nicolacimmino/PLC-14500/documentation/kit/rev.b/Kit Sleeve Back.pdf

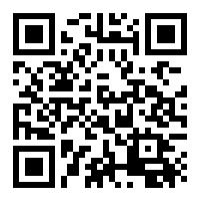
[picture p5: figure]

https://github.com/nicolacimmino/PLC-14500
