nicolacimmino/PLC-14500/_docs/board.jpg

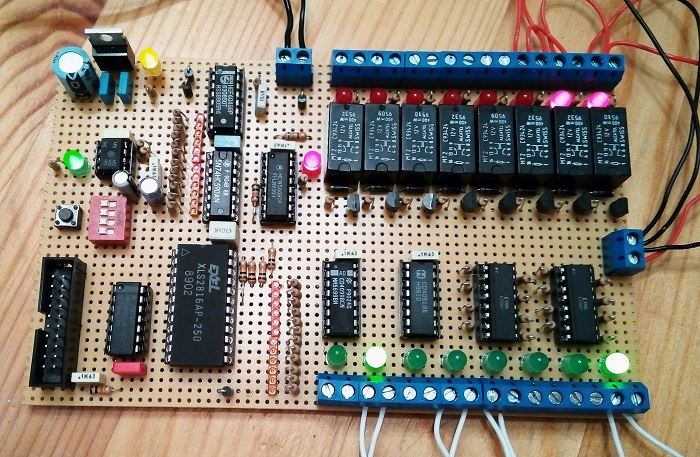
_docs/board.jpg
