nicolacimmino/PLC-14500/documentation/board.png

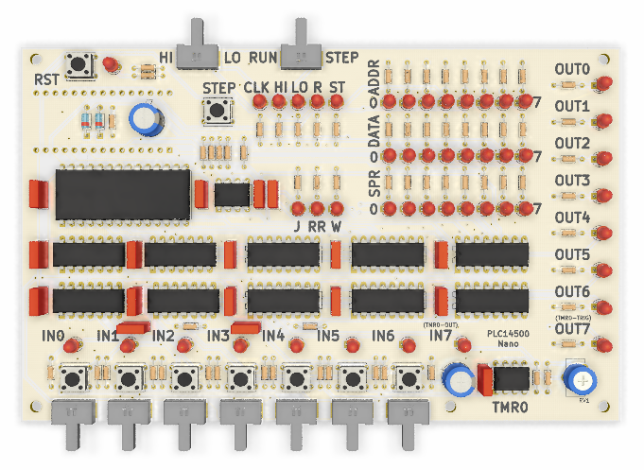
documentation/board.png
