nicolacimmino/PLC-14500/documentation/board_black_revd.png

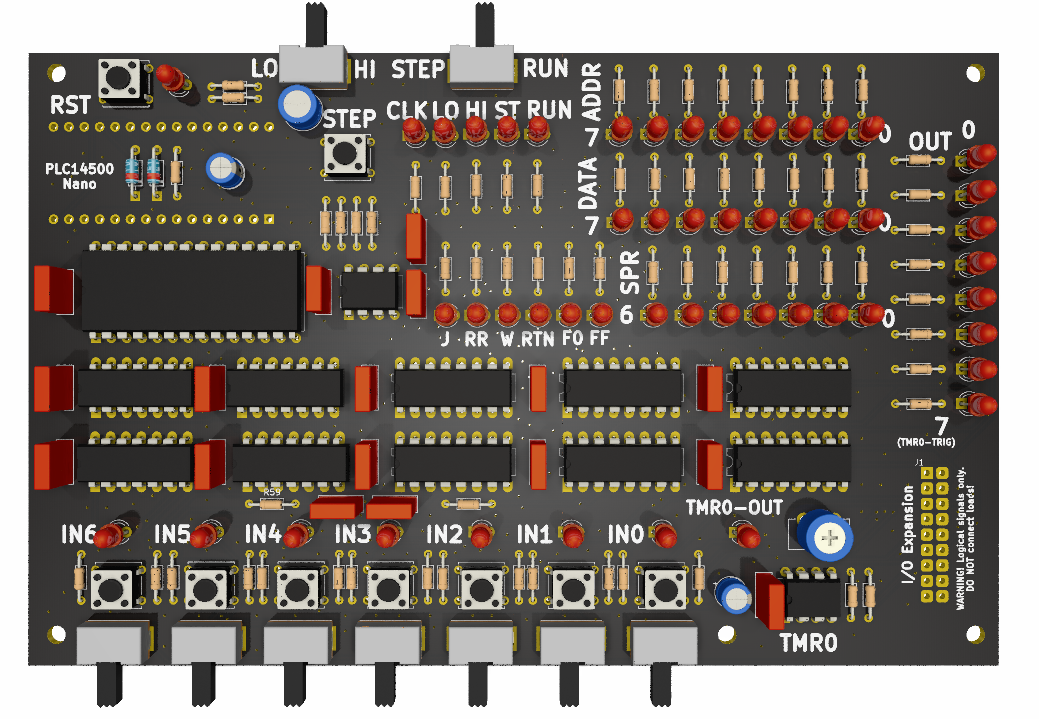
documentation/board_black_revd.png
