nicolacimmino/PLC-14500/documentation/board_green_revc.png

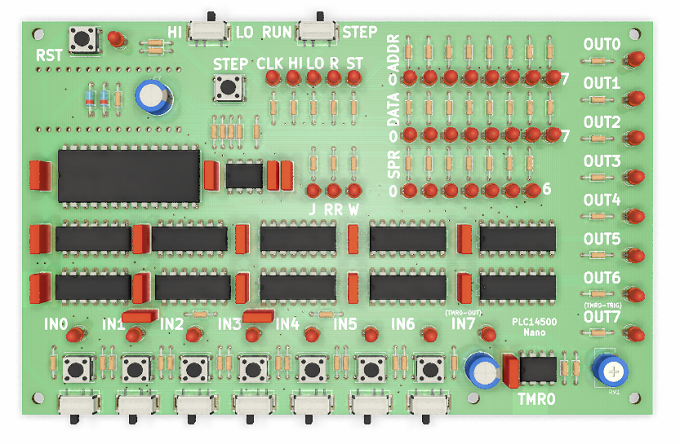
documentation/board_green_revc.png
