nicolacimmino/PLC-14500/documentation/board_white_revc.png

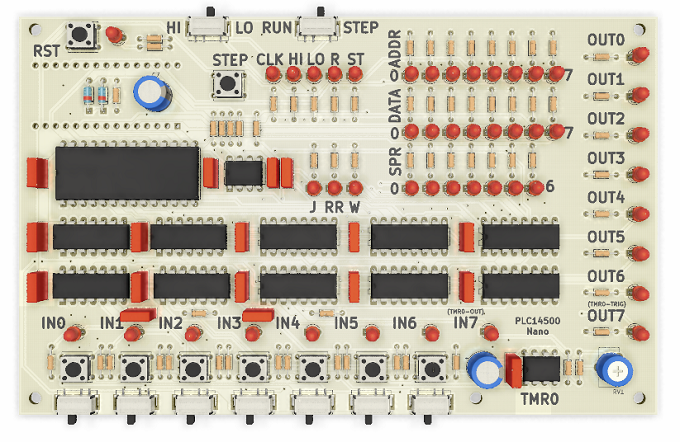
documentation/board_white_revc.png
