nicolacimmino/PLC-14500/documentation/ex1_load_and_store.png

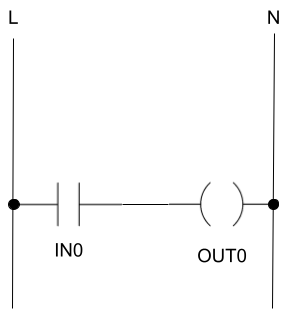
documentation/ex1_load_and_store.png
