nicolacimmino/PLC-14500/documentation/ex3_latch.png

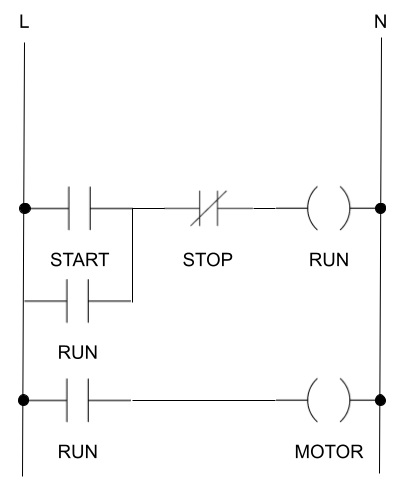
documentation/ex3_latch.png
