nicolacimmino/PLC-14500/documentation/ladder_coil.png

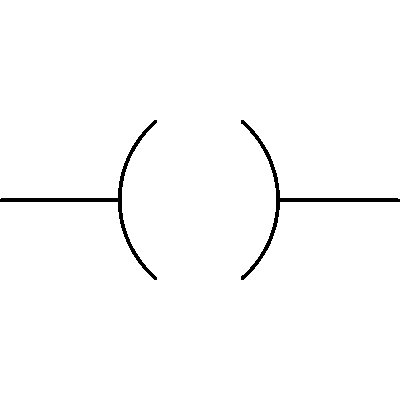
documentation/ladder_coil.png
