nicolacimmino/PLC-14500/documentation/ladder_nc.png

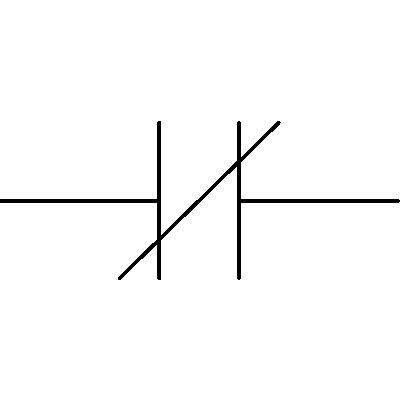
documentation/ladder_nc.png
