nicolacimmino/PLC-14500/documentation/oshw_cert.png

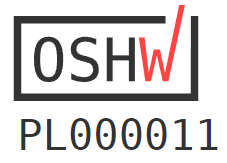
documentation/oshw_cert.png
