nicolacimmino/PLC-14500/documentation/Output.png

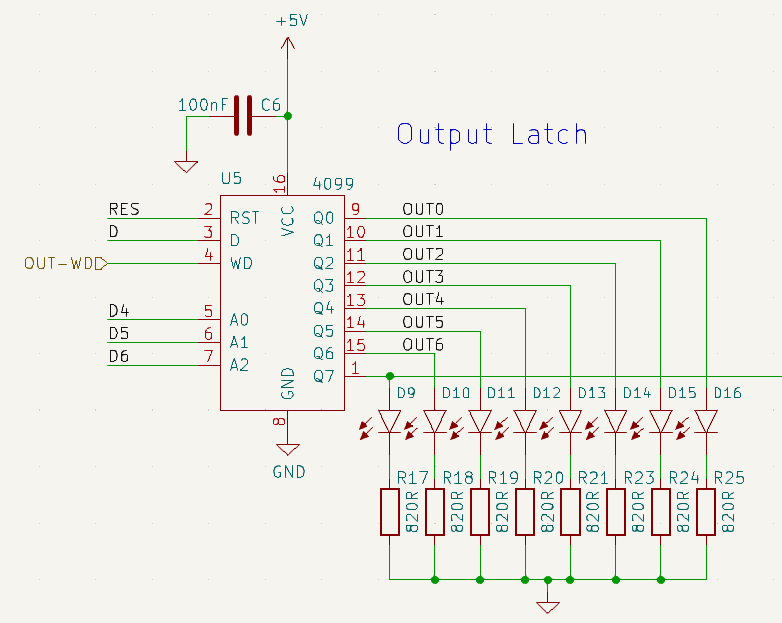
documentation/Output.png
