nicolacimmino/PLC-14500/documentation/pc_memory_icu.png

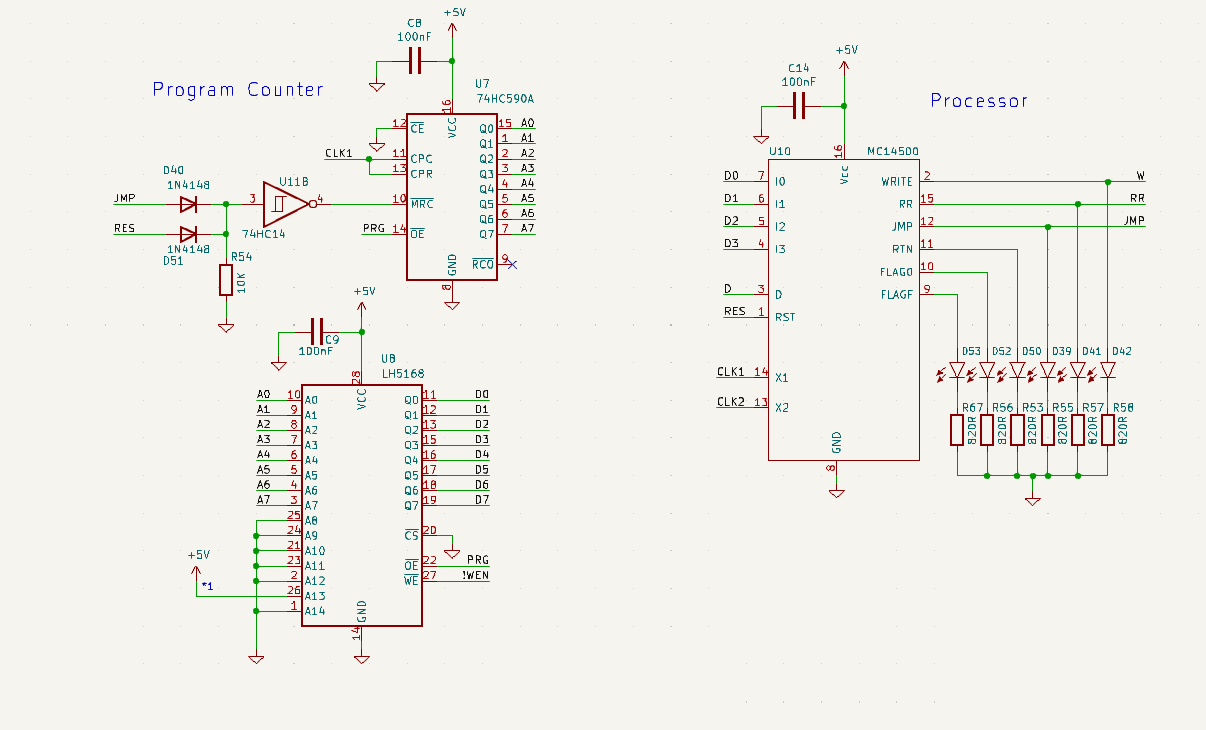
documentation/pc_memory_icu.png
