nicolacimmino/PLC-14500/documentation/PLC14500-Nano_IO_Map.png

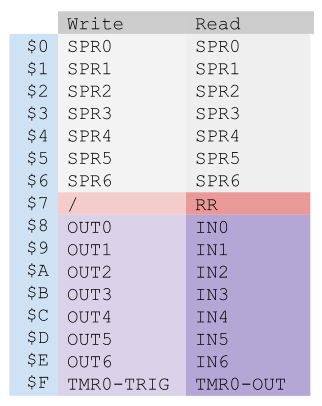
documentation/PLC14500-Nano_IO_Map.png
