nicolacimmino/PLC-14500/documentation/Pulse.png

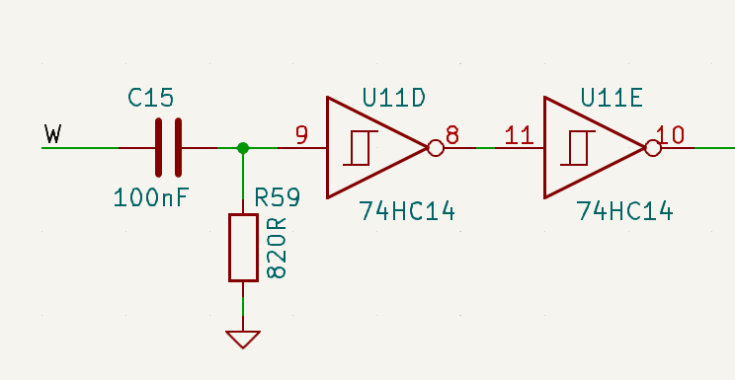
documentation/Pulse.png
