nicolacimmino/PLC-14500/documentation/scop_wp_d4.png

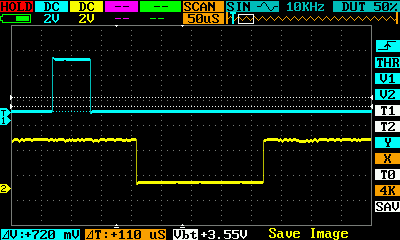
documentation/scop_wp_d4.png
