nicolacimmino/PLC-14500/documentation/scope_w_d4.png

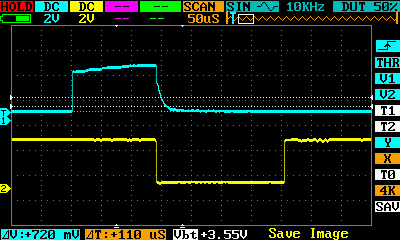
documentation/scope_w_d4.png
