nicolacimmino/PLC-14500/documentation/scope_w_wp.png

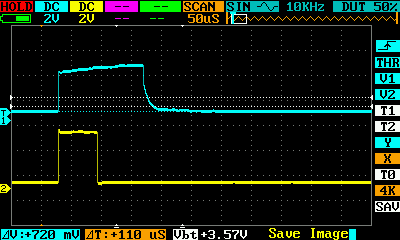
documentation/scope_w_wp.png
