nicolacimmino/PLC-14500/documentation/simulator.png

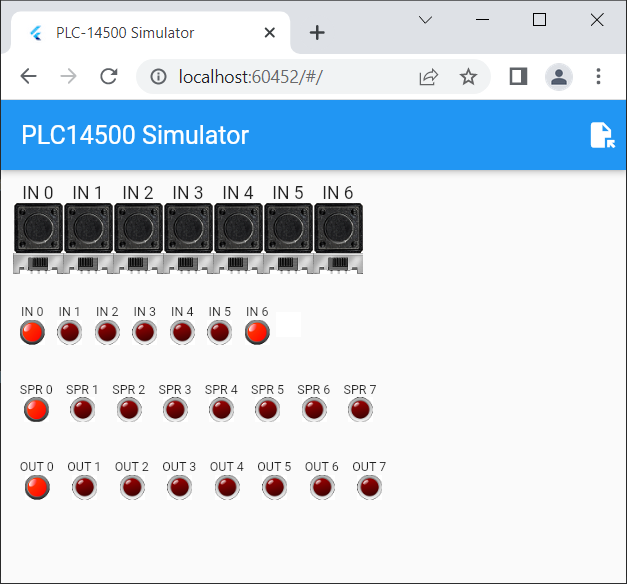
documentation/simulator.png
