nicolacimmino/PLC-14500/documentation/wconditioning.png

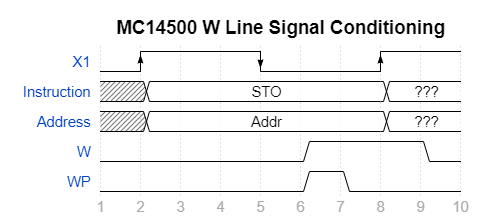
documentation/wconditioning.png
