nicolacimmino/PLC-14500/documentation/kit/rev.b/Assembly Plan.pdf

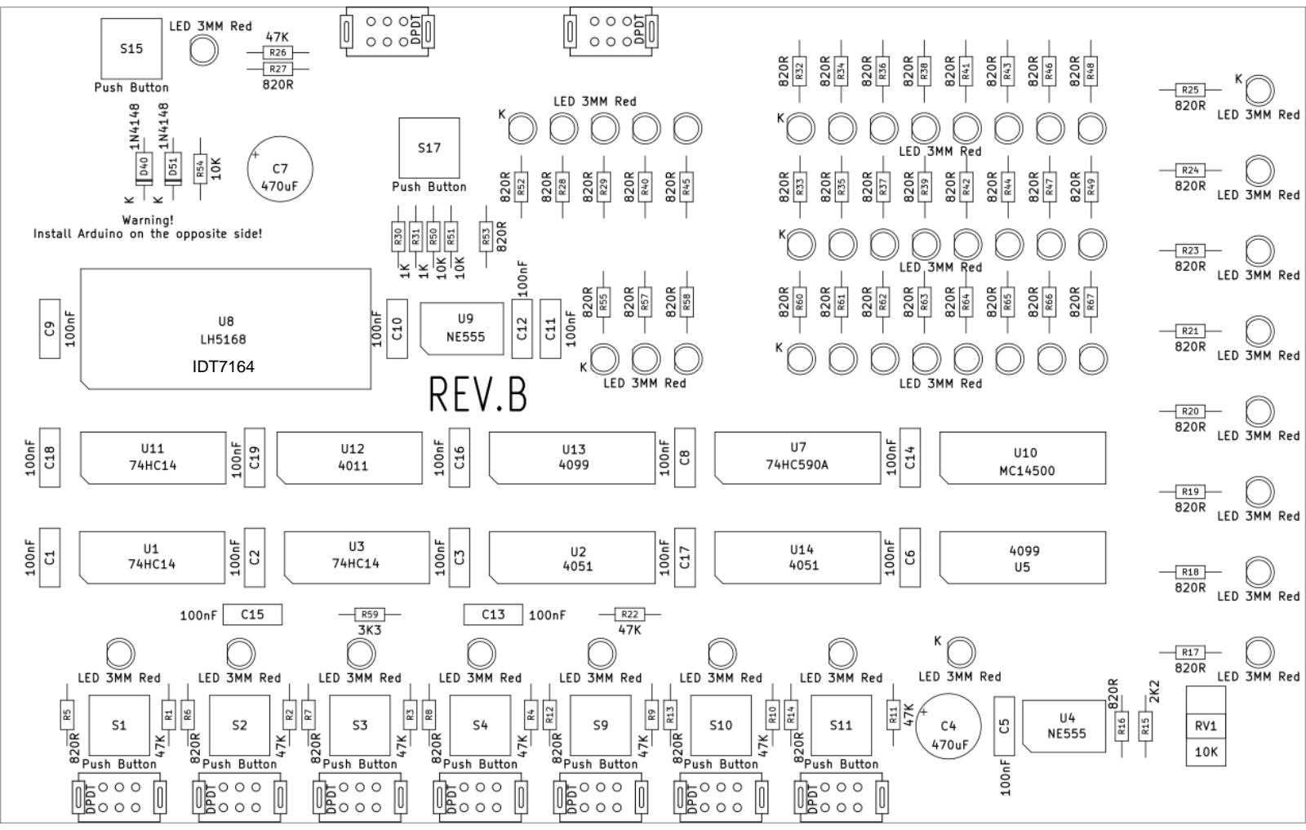
[picture p35: page 1]
