nicolacimmino/PLC-14500/documentation/kit/rev.c/BOM.pdf

# PLC14500 - Nano REV.C

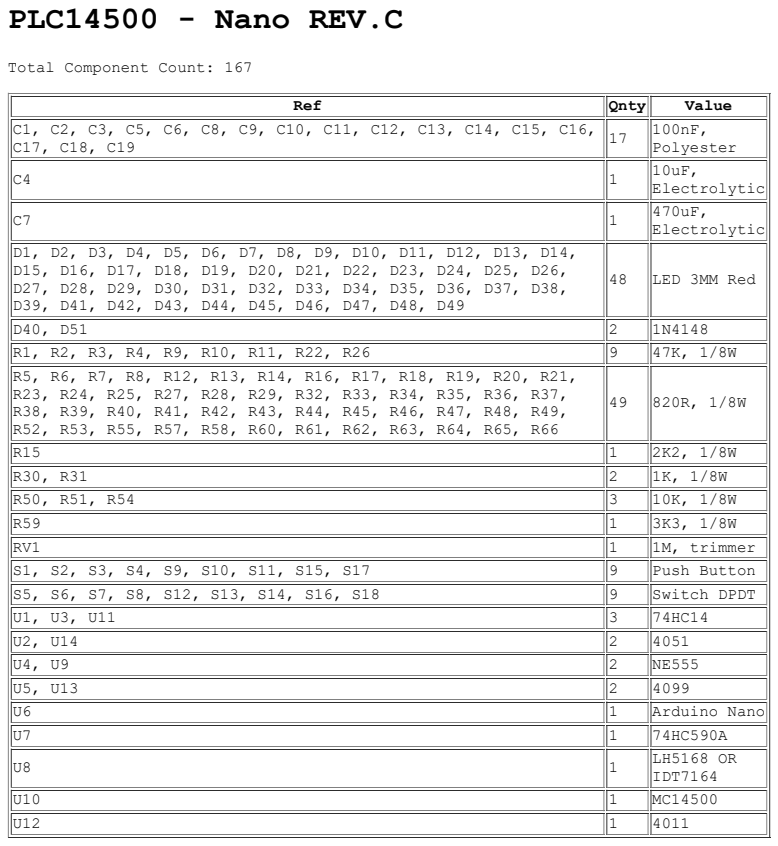
[picture p57: page 1]
